dst78/planck/vOctTable.h

// custom tuning
// baseNote used: 32.6600
// baseIncr used: 1.9550
const uint16_t freqTable[] PROGMEM = {
68, 
69, 69, 69, 69, 70, 70, 70, 70, 71, 71, 
71, 71, 71, 72, 72, 72, 72, 73, 73, 73, 
73, 74, 74, 74, 74, 75, 75, 75, 75, 76, 
76, 76, 76, 77, 77, 77, 77, 78, 78, 78, 
78, 79, 79, 79, 79, 80, 80, 80, 80, 81, 
81, 81, 81, 82, 82, 82, 83, 83, 83, 83, 
84, 84, 84, 84, 85, 85, 85, 86, 86, 86, 
86, 87, 87, 87, 88, 88, 88, 88, 89, 89, 
89, 90, 90, 90, 90, 91, 91, 91, 92, 92, 
92, 93, 93, 93, 93, 94, 94, 94, 95, 95, 
95, 96, 96, 96, 97, 97, 97, 98, 98, 98, 
99, 99, 99, 99, 100, 100, 100, 101, 101, 101, 
102, 102, 102, 103, 103, 103, 104, 104, 104, 105, 
105, 106, 106, 106, 107, 107, 107, 108, 108, 108, 
109, 109, 109, 110, 110, 110, 111, 111, 112, 112, 
112, 113, 113, 113, 114, 114, 115, 115, 115, 116, 
116, 116, 117, 117, 118, 118, 118, 119, 119, 119, 
120, 120, 121, 121, 121, 122, 122, 123, 123, 123, 
124, 124, 125, 125, 126, 126, 126, 127, 127, 128, 
128, 128, 129, 129, 130, 130, 131, 131, 131, 132, 
132, 133, 133, 134, 134, 134, 135, 135, 136, 136, 
137, 137, 138, 138, 138, 139, 139, 140, 140, 141, 
141, 142, 142, 143, 143, 144, 144, 144, 145, 145, 
146, 146, 147, 147, 148, 148, 149, 149, 150, 150, 
151, 151, 152, 152, 153, 153, 154, 154, 155, 155, 
156, 156, 157, 157, 158, 158, 159, 159, 160, 160, 
161, 161, 162, 163, 163, 164, 164, 165, 165, 166, 
166, 167, 167, 168, 168, 169, 170, 170, 171, 171, 
172, 172, 173, 174, 174, 175, 175, 176, 176, 177, 
178, 178, 179, 179, 180, 180, 181, 182, 182, 183, 
183, 184, 185, 185, 186, 186, 187, 188, 188, 189, 
190, 190, 191, 191, 192, 193, 193, 194, 195, 195, 
196, 197, 197, 198, 198, 199, 200, 200, 201, 202, 
202, 203, 204, 204, 205, 206, 206, 207, 208, 208, 
209, 210, 211, 211, 212, 213, 213, 214, 215, 215, 
216, 217, 218, 218, 219, 220, 220, 221, 222, 223, 
223, 224, 225, 225, 226, 227, 228, 228, 229, 230, 
231, 231, 232, 233, 234, 235, 235, 236, 237, 238, 
238, 239, 240, 241, 242, 242, 243, 244, 245, 246, 
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
};
